LarsBachmann/Seilsender/media/ScrPiJuiceSettingsHatConfigFirmware.png

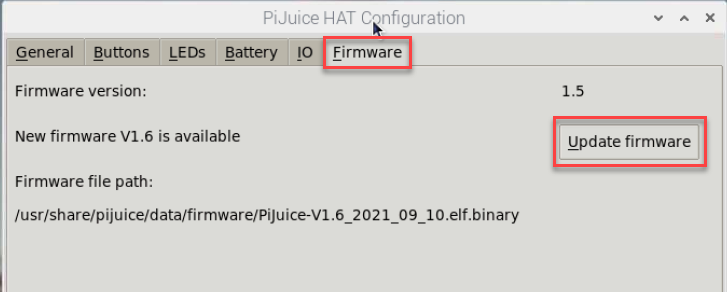
media/ScrPiJuiceSettingsHatConfigFirmware.png
