LarsBachmann/Seilsender/media/ScrPiJuiceSettingsHatConfigGeneral.png

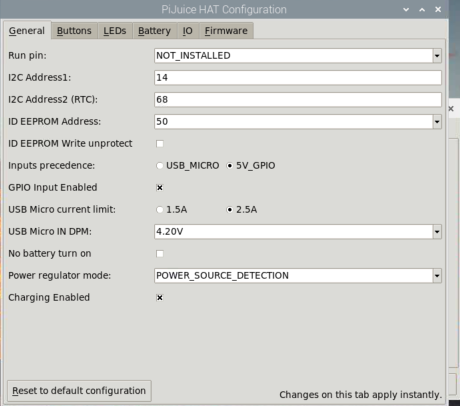
media/ScrPiJuiceSettingsHatConfigGeneral.png
