LarsBachmann/Seilsender/media/ScrPiJuiceSettingsUserScripts2.png

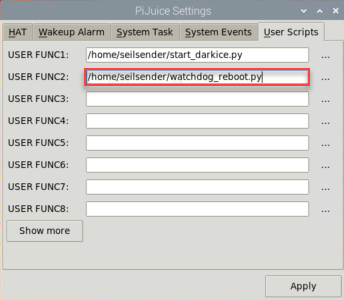
media/ScrPiJuiceSettingsUserScripts2.png
