LarsBachmann/Seilsender/media/VisatonScrewClamp.png

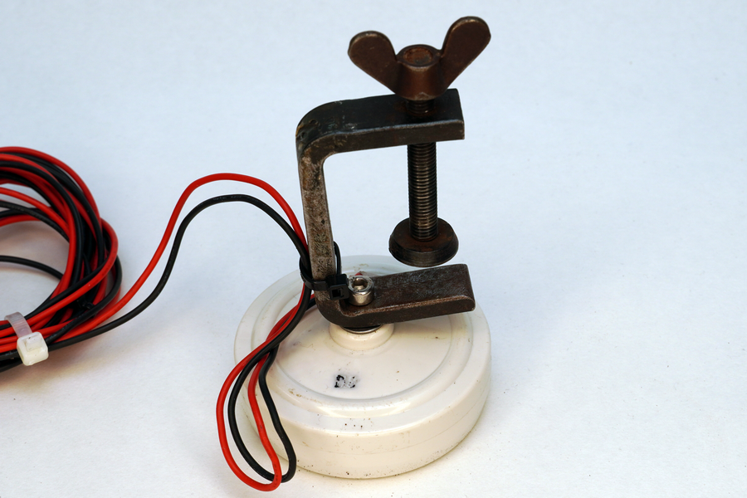
media/VisatonScrewClamp.png
